palmacas/PICKit2_Clone/ZIF_Distribution/40pin PIC.png

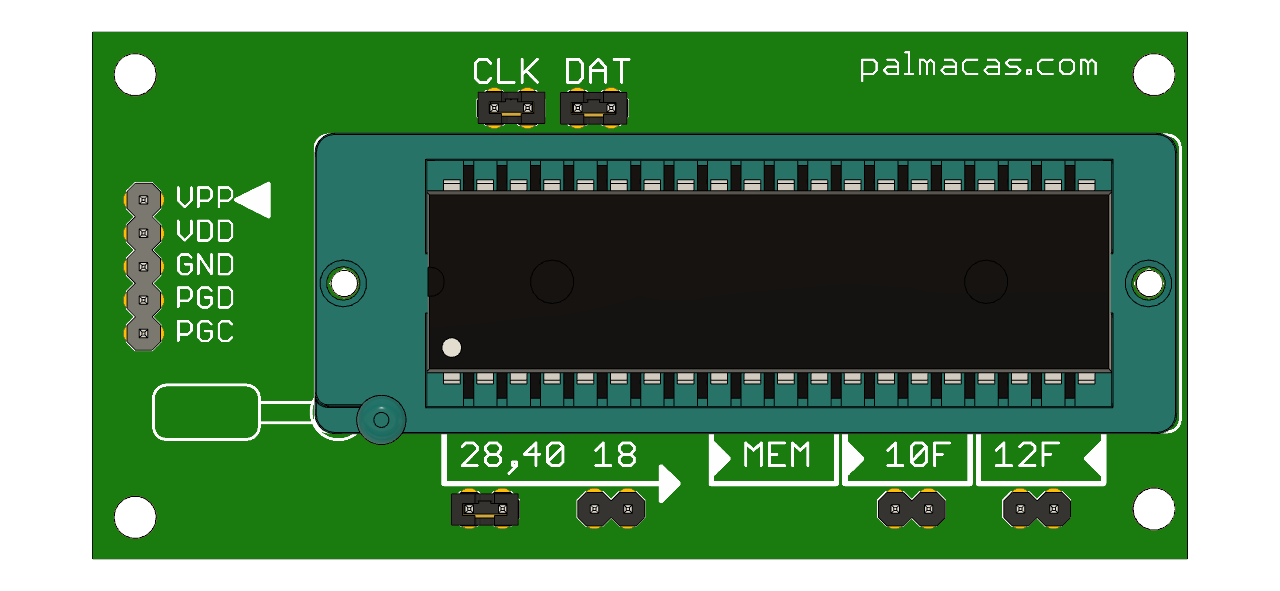
ZIF_Distribution/40pin PIC.png
